4rcan31/FTechnolgy/Croquette/images/Z.png

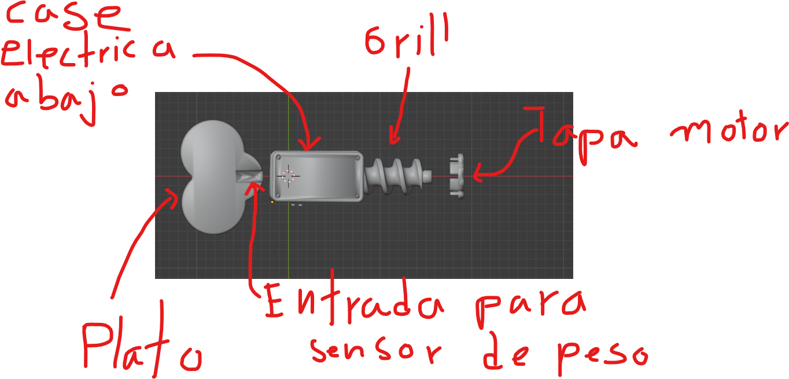
Croquette/images/Z.png
