4rcan31/FTechnolgy/Docs/ModelCanvas.png

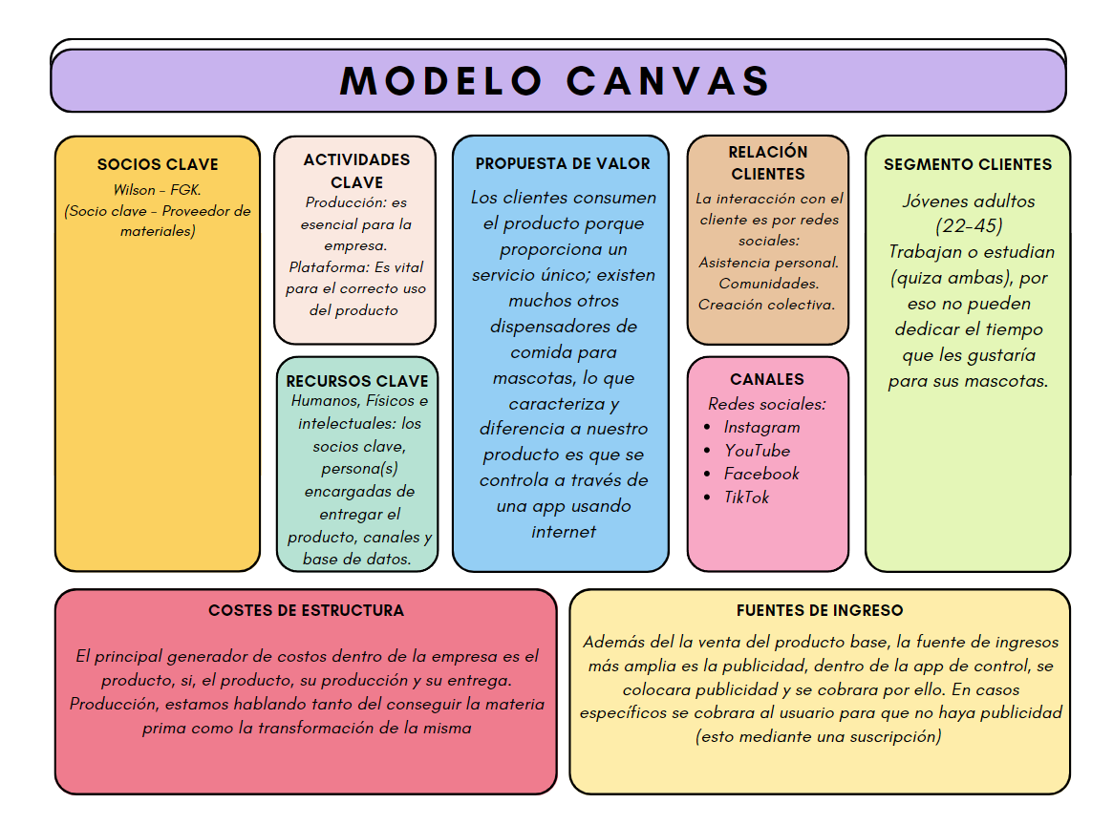
Docs/ModelCanvas.png
